RicardoMarquesCardoso/MicroLab/Microscope/Designs/[Top]Part1.DXF

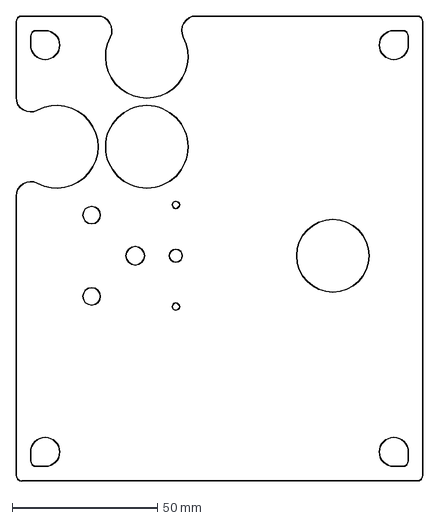
[picture p34: CAD file, 2020-10-22]
Microscope/Designs/[Top]Part1.DXF
140.0 x 160.0 mm
