RicardoMarquesCardoso/MicroLab/SyringePumps/Designs/Syringeholder2.DXF

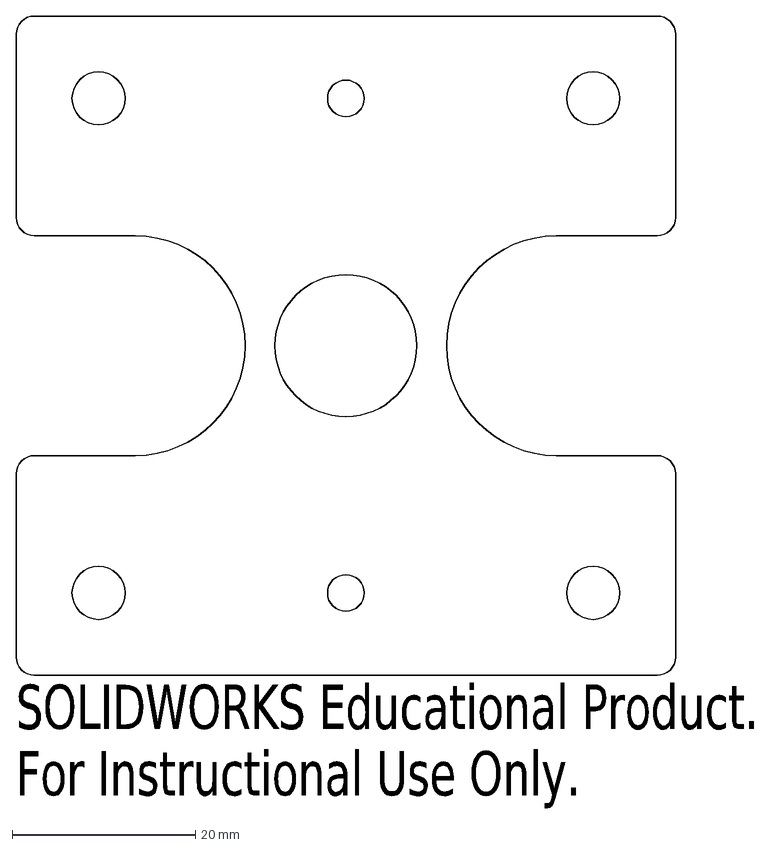
[picture p35: CAD file, 2020-11-19]
SyringePumps/Designs/Syringeholder2.DXF
SOLIDWORKS Educational Product.
For Instructional Use Only.
