RicardoMarquesCardoso/MicroLab/SyringePumps/Parts/Adapters/18mm.SLDPRT

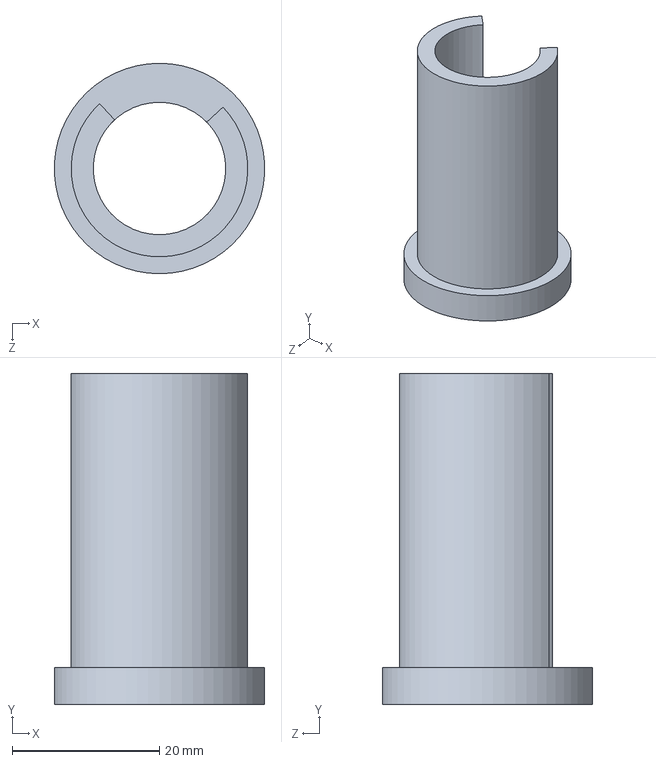
[picture p36: CAD file, 2020-11-19]
SyringePumps/Parts/Adapters/18mm.SLDPRT
28.6 x 45.0 x 28.6 mm
