RicardoMarquesCardoso/MicroLab/SyringePumps/Parts/MotorTop.SLDPRT

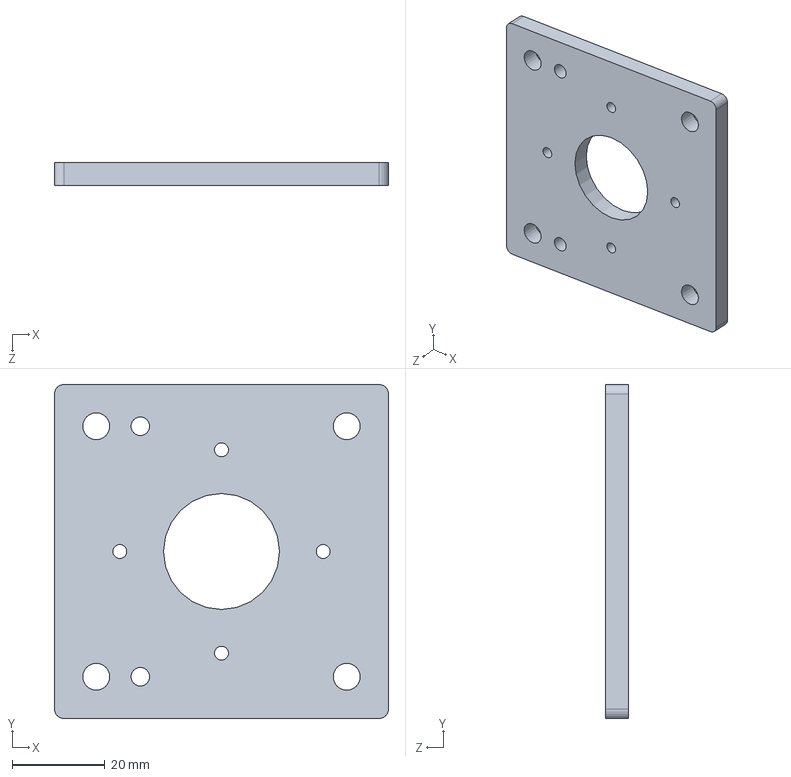
[picture p37: CAD file, 2020-11-19]
SyringePumps/Parts/MotorTop.SLDPRT
72.0 x 72.0 x 5.00 mm
