RicardoMarquesCardoso/MicroLab/Microscope/Designs/[MovingPiece]Top2.DXF

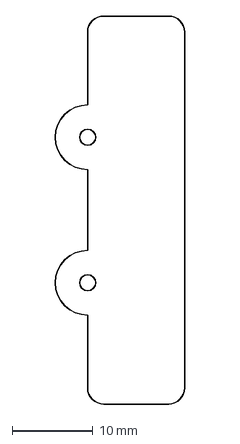
[picture p38: CAD file, 2020-10-22]
Microscope/Designs/[MovingPiece]Top2.DXF
16.0 x 48.0 mm
