RicardoMarquesCardoso/MicroLab/Microscope/Parts/Light.SLDPRT

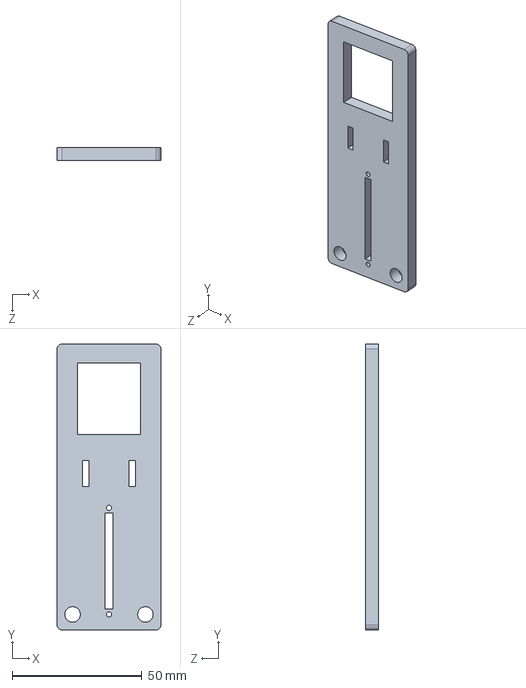
[picture p39: CAD file, 2020-10-22]
Microscope/Parts/Light.SLDPRT
40.0 x 110.0 x 5.00 mm
