RicardoMarquesCardoso/MicroLab/SyringePumps/Designs/MotorTop.DXF

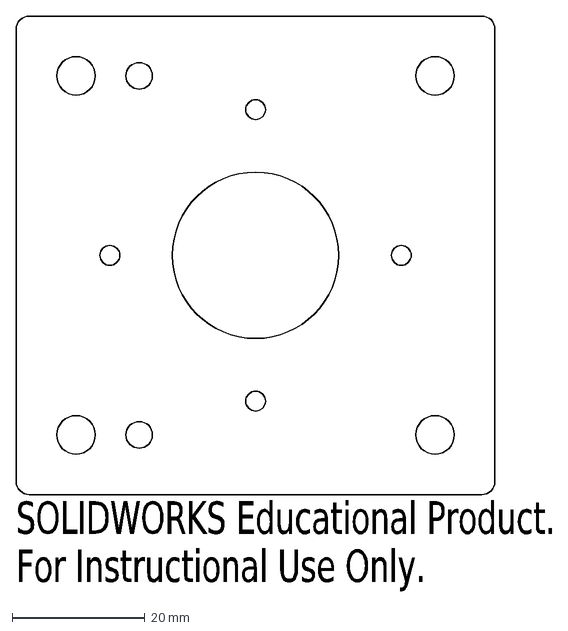
[picture p40: CAD file, 2020-11-19]
SyringePumps/Designs/MotorTop.DXF
SOLIDWORKS Educational Product.
For Instructional Use Only.
