RicardoMarquesCardoso/MicroLab/SyringePumps/Parts/movingpart2.SLDPRT

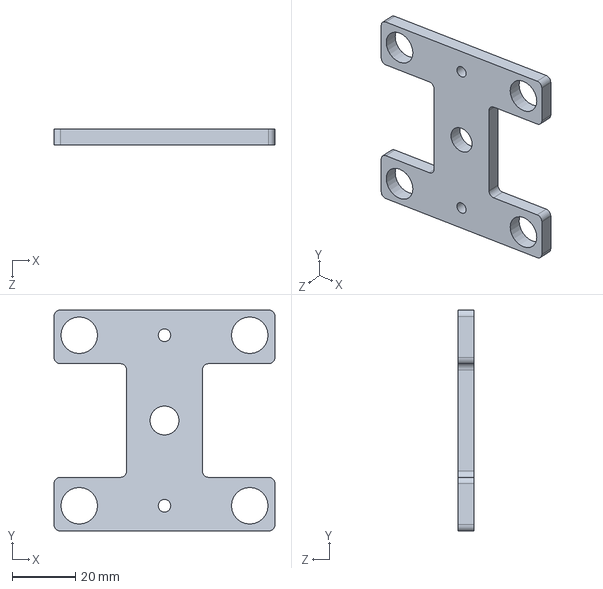
[picture p41: CAD file, 2020-11-19]
SyringePumps/Parts/movingpart2.SLDPRT
70.0 x 70.0 x 5.00 mm
