RicardoMarquesCardoso/MicroLab/Microscope/Designs/Light.DXF

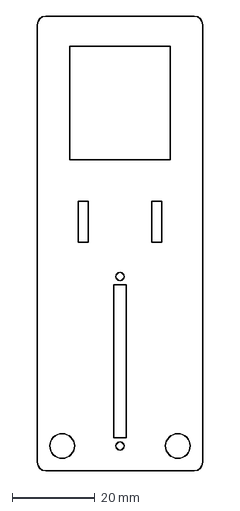
[picture p42: CAD file, 2020-10-22]
Microscope/Designs/Light.DXF
40.0 x 110.0 mm
