RicardoMarquesCardoso/MicroLab/Microscope/Parts/Bearing(LM6UU).SLDPRT

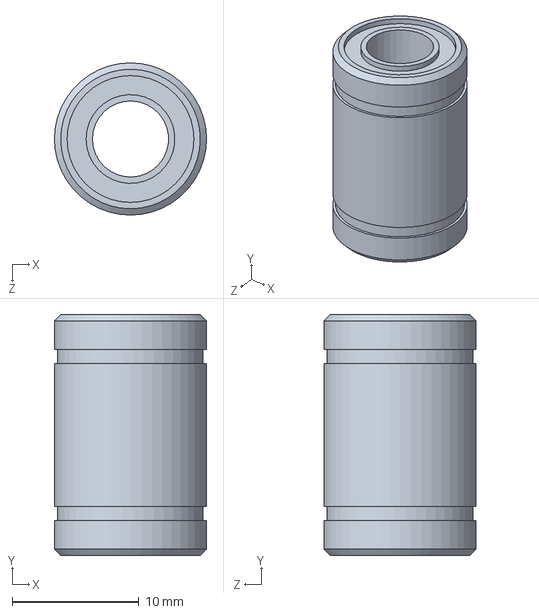
[picture p43: CAD file, 2020-10-22]
Microscope/Parts/Bearing(LM6UU).SLDPRT
12.0 x 19.0 x 12.0 mm
