RicardoMarquesCardoso/MicroLab/SyringePumps/Designs/movingpart.DXF

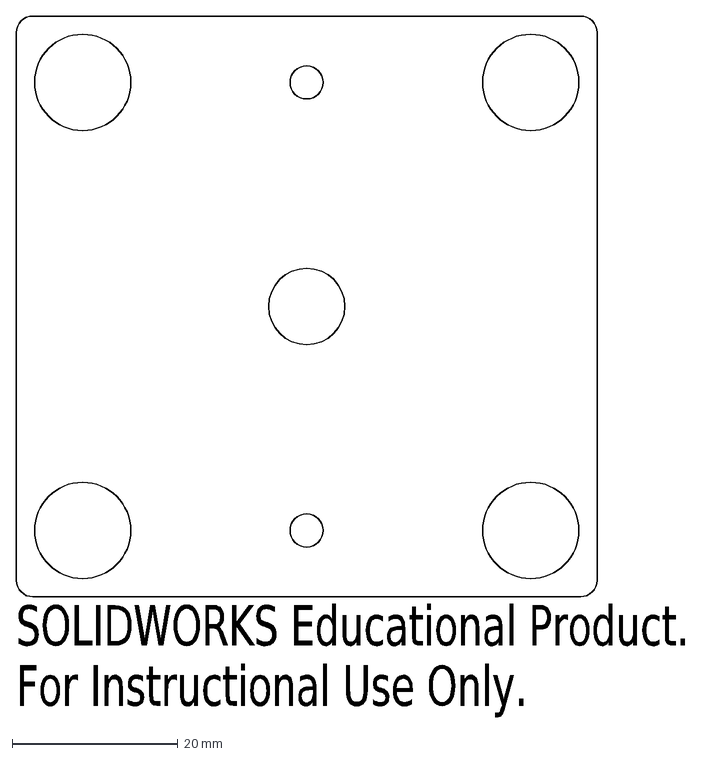
[picture p44: CAD file, 2020-11-19]
SyringePumps/Designs/movingpart.DXF
SOLIDWORKS Educational Product.
For Instructional Use Only.
