RicardoMarquesCardoso/MicroLab/SyringePumps/Parts/bar(35cm).SLDPRT

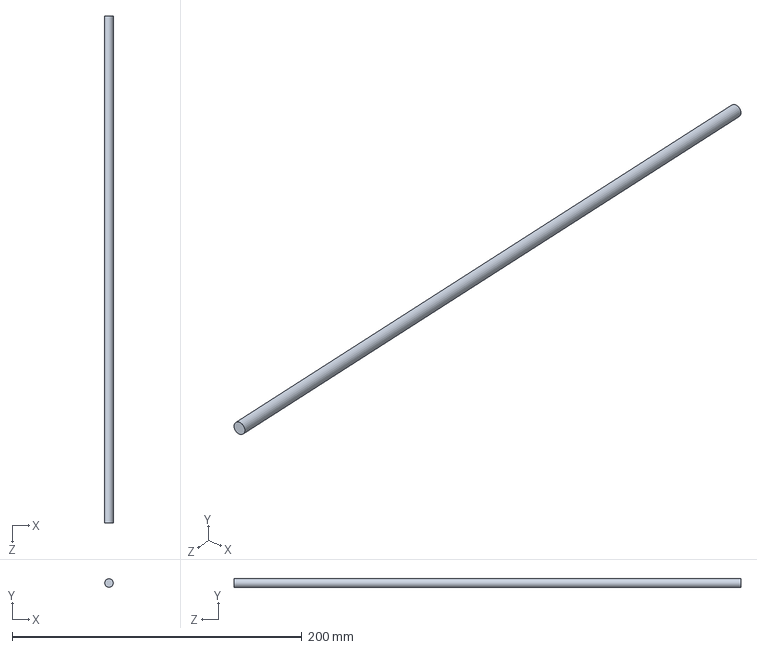
[picture p45: CAD file, 2020-11-19]
SyringePumps/Parts/bar(35cm).SLDPRT
6.00 x 6.00 x 350.0 mm
