RicardoMarquesCardoso/MicroLab/Microscope/Designs/[MovingPiece]Bottom.DXF

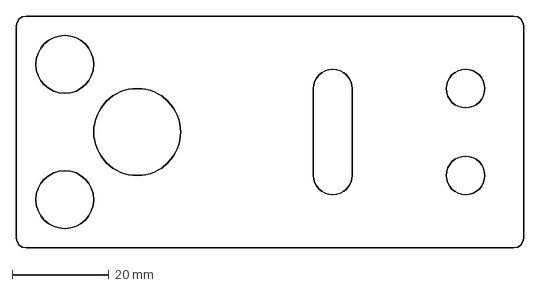
[picture p46: CAD file, 2020-10-22]
Microscope/Designs/[MovingPiece]Bottom.DXF
105.0 x 48.0 mm
