RicardoMarquesCardoso/MicroLab/Microscope/Parts/Bar7cm.SLDPRT

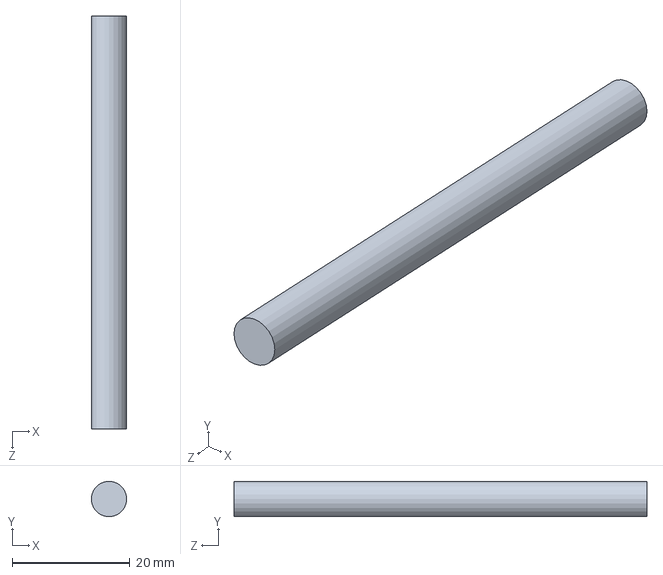
[picture p47: CAD file, 2020-10-22]
Microscope/Parts/Bar7cm.SLDPRT
6.00 x 6.00 x 70.0 mm
