RicardoMarquesCardoso/MicroLab/SyringePumps/Designs/Syringeholder1.DXF

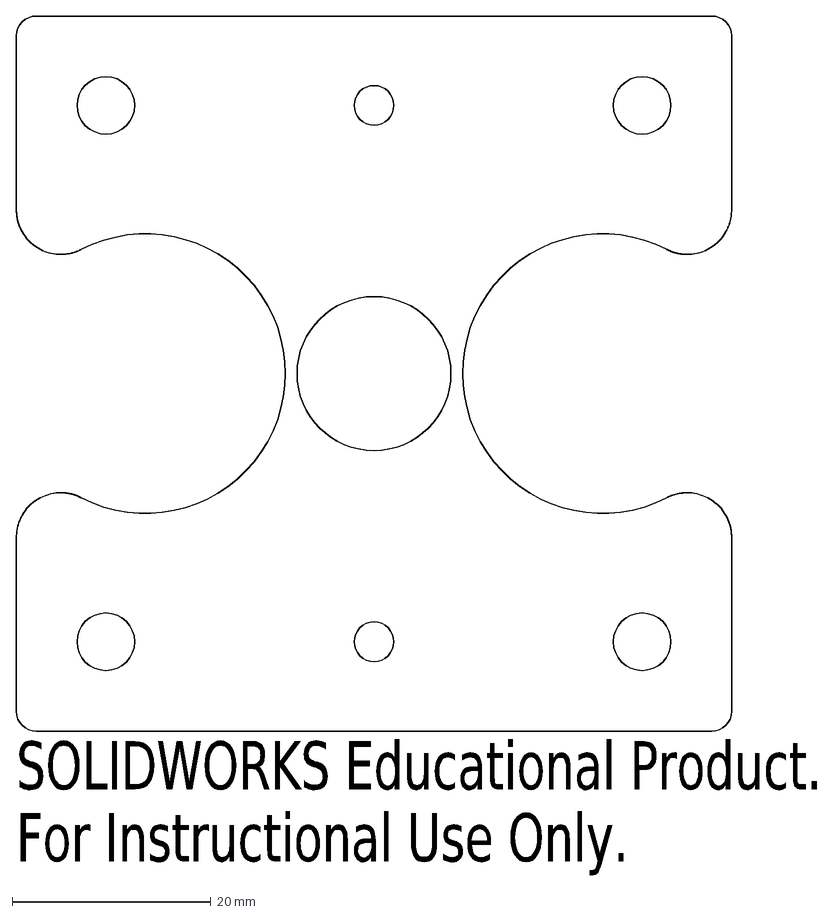
[picture p48: CAD file, 2020-11-19]
SyringePumps/Designs/Syringeholder1.DXF
SOLIDWORKS Educational Product.
For Instructional Use Only.
