RicardoMarquesCardoso/MicroLab/SyringePumps/Parts/Syringeholder1.SLDPRT

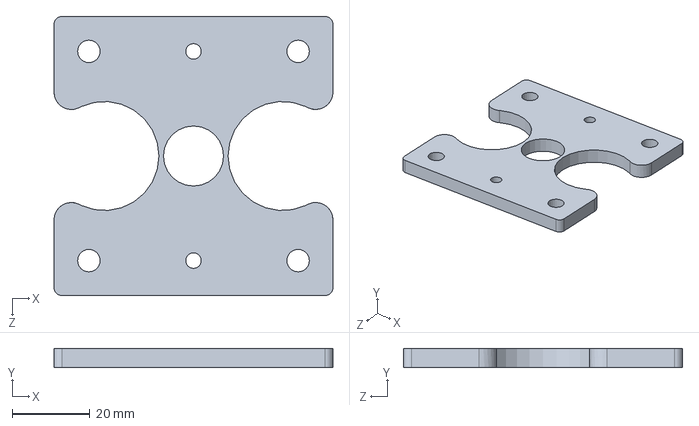
[picture p49: CAD file, 2020-11-19]
SyringePumps/Parts/Syringeholder1.SLDPRT
72.0 x 5.00 x 72.0 mm
