RicardoMarquesCardoso/MicroLab/Microscope/Parts/[MovingPiece]Bottom.SLDPRT

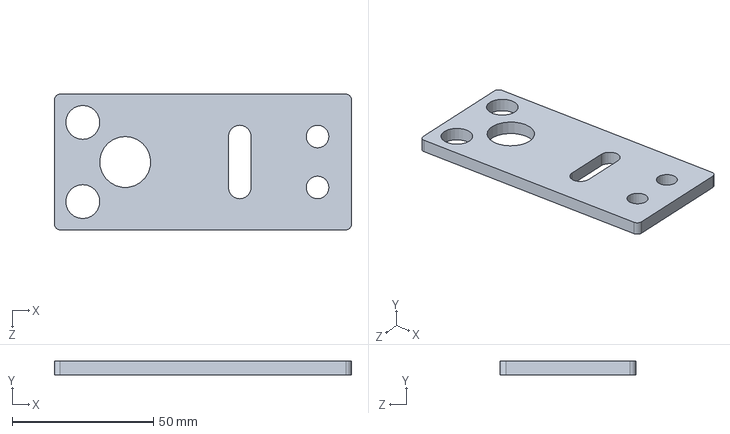
[picture p50: CAD file, 2020-10-22]
Microscope/Parts/[MovingPiece]Bottom.SLDPRT
105.0 x 5.00 x 48.0 mm
