RicardoMarquesCardoso/MicroLab/SyringePumps/Parts/syringeholder3.SLDPRT

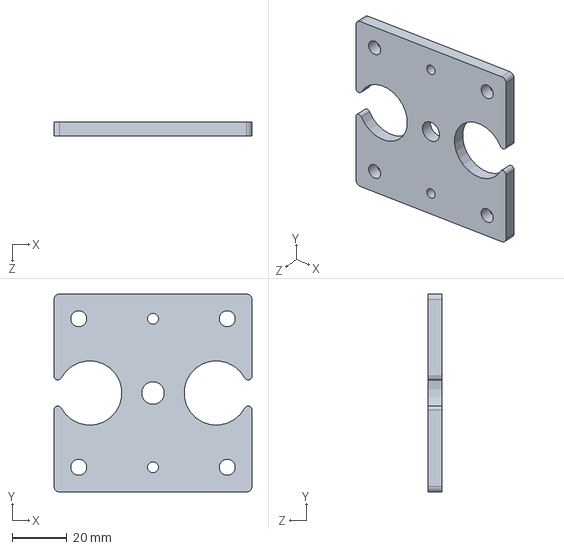
[picture p51: CAD file, 2020-11-19]
SyringePumps/Parts/syringeholder3.SLDPRT
72.0 x 72.0 x 5.00 mm
