RicardoMarquesCardoso/MicroLab/Microscope/Parts/[Top]Part2.SLDPRT

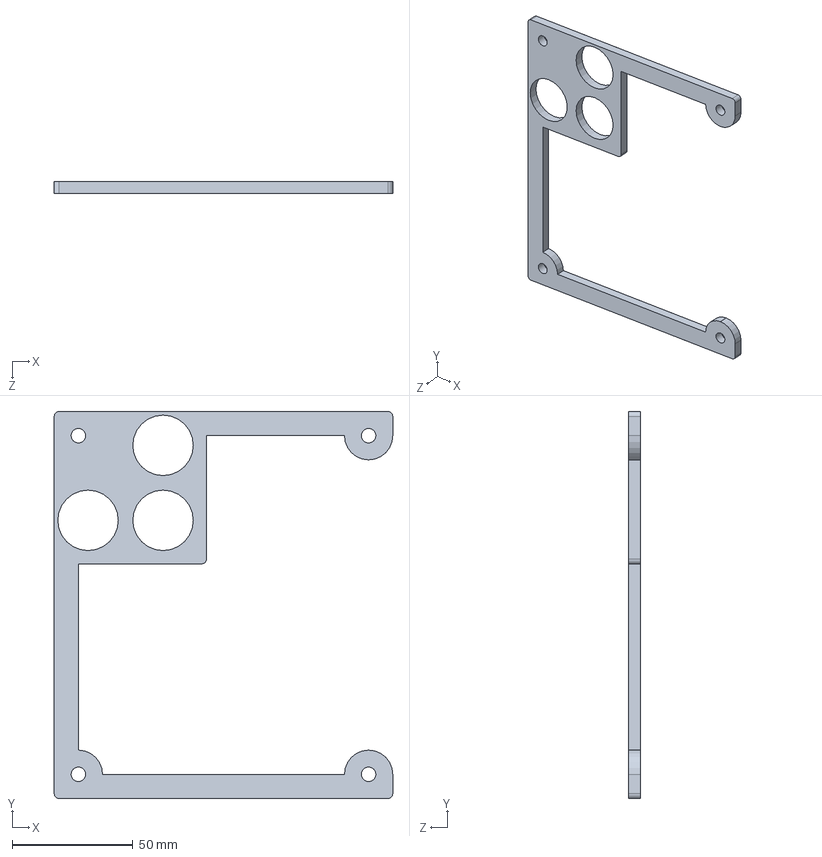
[picture p52: CAD file, 2020-10-22]
Microscope/Parts/[Top]Part2.SLDPRT
140.0 x 160.0 x 5.00 mm
