RicardoMarquesCardoso/MicroLab/Microscope/Parts/[MovingPiece]Top2.SLDPRT

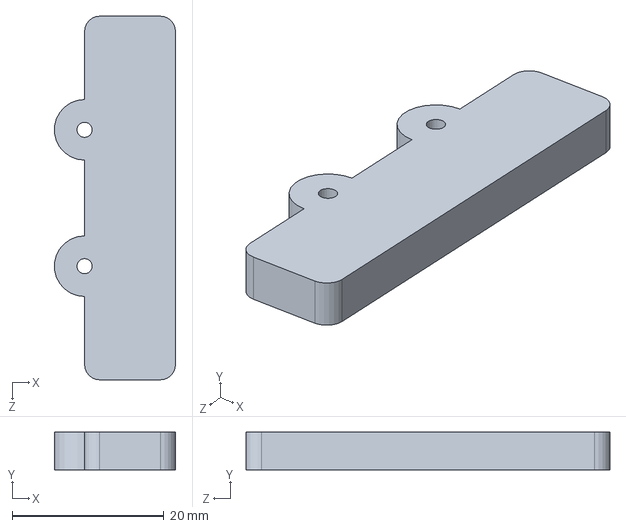
[picture p53: CAD file, 2020-10-22]
Microscope/Parts/[MovingPiece]Top2.SLDPRT
16.0 x 5.00 x 48.0 mm
