RicardoMarquesCardoso/MicroLab/SyringePumps/Parts/MotorBot2.SLDPRT

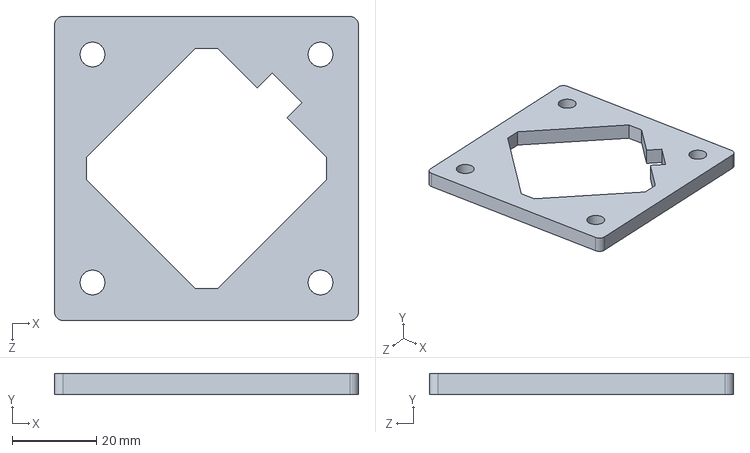
[picture p54: CAD file, 2020-11-19]
SyringePumps/Parts/MotorBot2.SLDPRT
72.0 x 5.00 x 72.0 mm
