RicardoMarquesCardoso/MicroLab/Microscope/Parts/[Top]Part1.SLDPRT

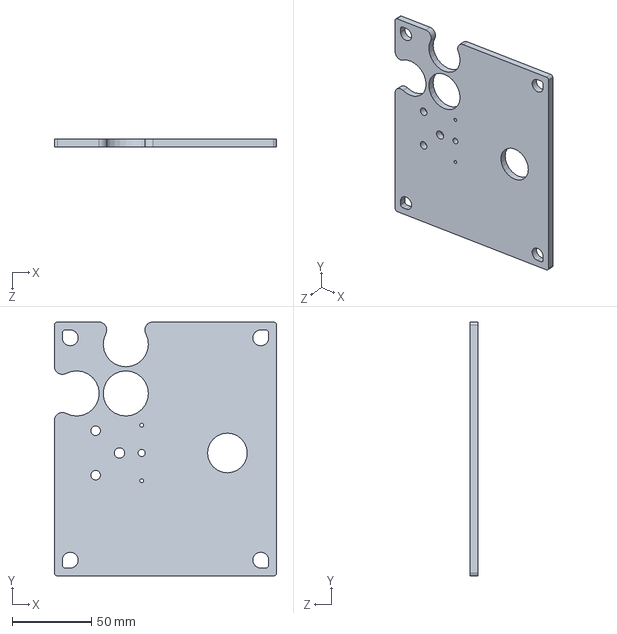
[picture p55: CAD file, 2020-10-22]
Microscope/Parts/[Top]Part1.SLDPRT
140.0 x 160.0 x 5.00 mm
