RicardoMarquesCardoso/MicroLab/Microscope/Parts/Nut(N80L5P).sldprt

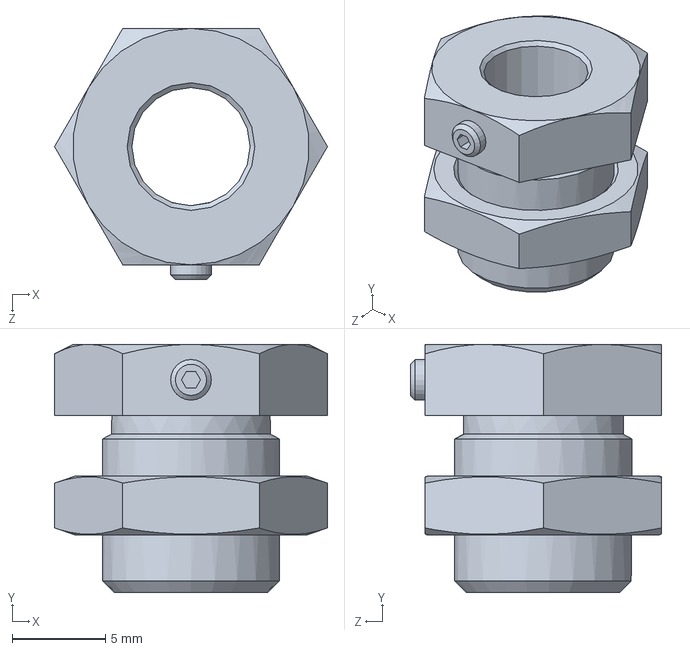
[picture p56: CAD file, 2020-10-22]
Microscope/Parts/Nut(N80L5P).sldprt
14.7 x 13.3 x 13.5 mm
