RicardoMarquesCardoso/MicroLab/Microscope/Parts/BottomPart.SLDPRT

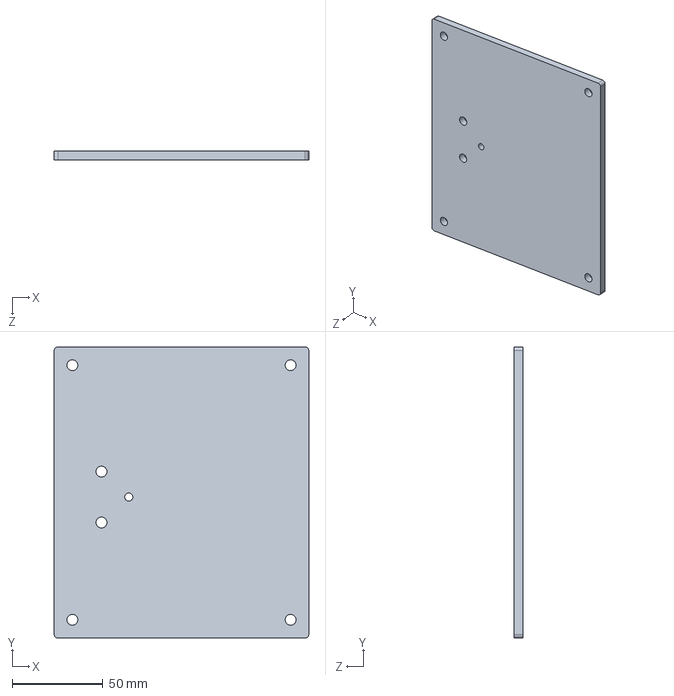
[picture p57: CAD file, 2020-10-22]
Microscope/Parts/BottomPart.SLDPRT
140.0 x 160.0 x 5.00 mm
