RicardoMarquesCardoso/MicroLab/Microscope/Parts/Collets.SLDPRT

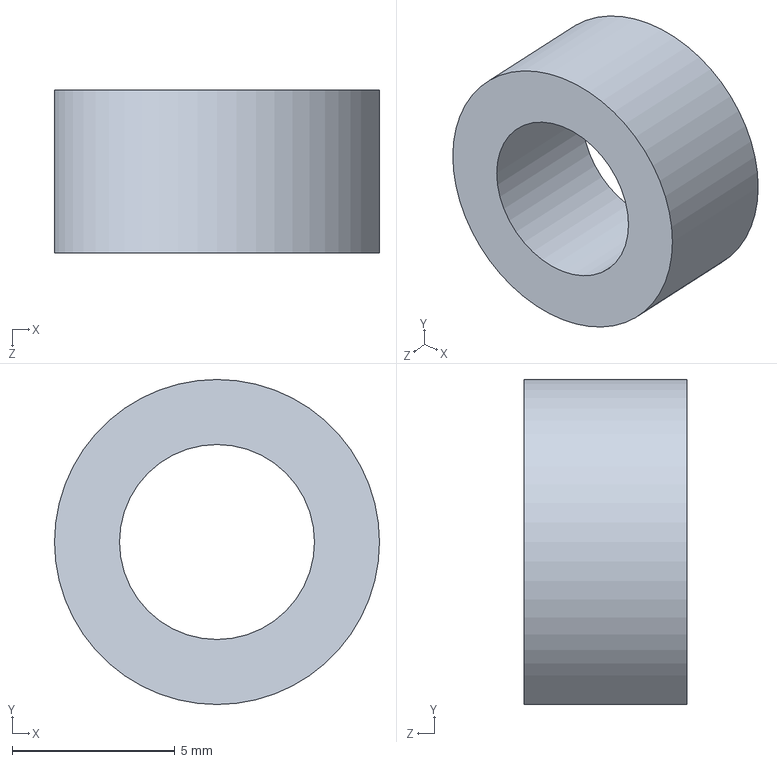
[picture p58: CAD file, 2020-10-22]
Microscope/Parts/Collets.SLDPRT
10.0 x 10.0 x 5.00 mm
