RicardoMarquesCardoso/MicroLab/Microscope/Parts/[PSeye]Part2.SLDPRT

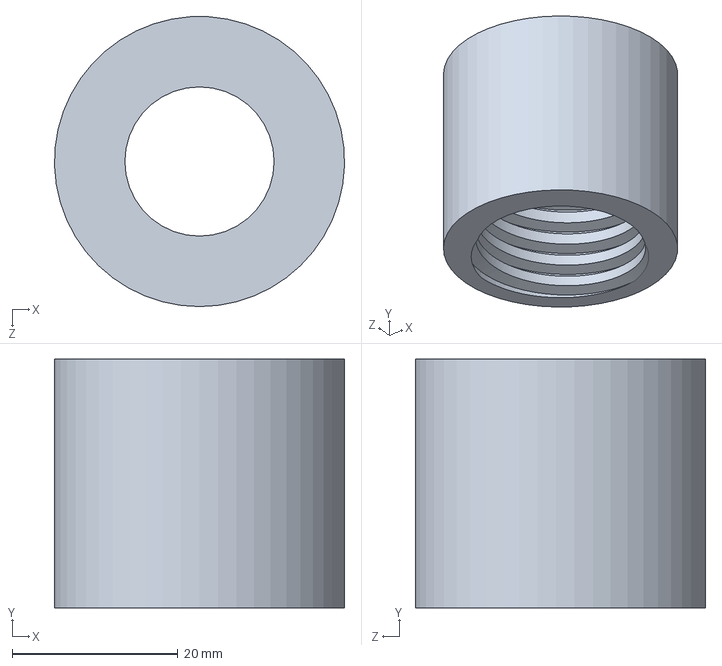
[picture p59: CAD file, 2020-10-01]
Microscope/Parts/[PSeye]Part2.SLDPRT
35.0 x 30.0 x 35.0 mm
