RicardoMarquesCardoso/MicroLab/Microscope/Parts/[PSeye]Part1.SLDPRT

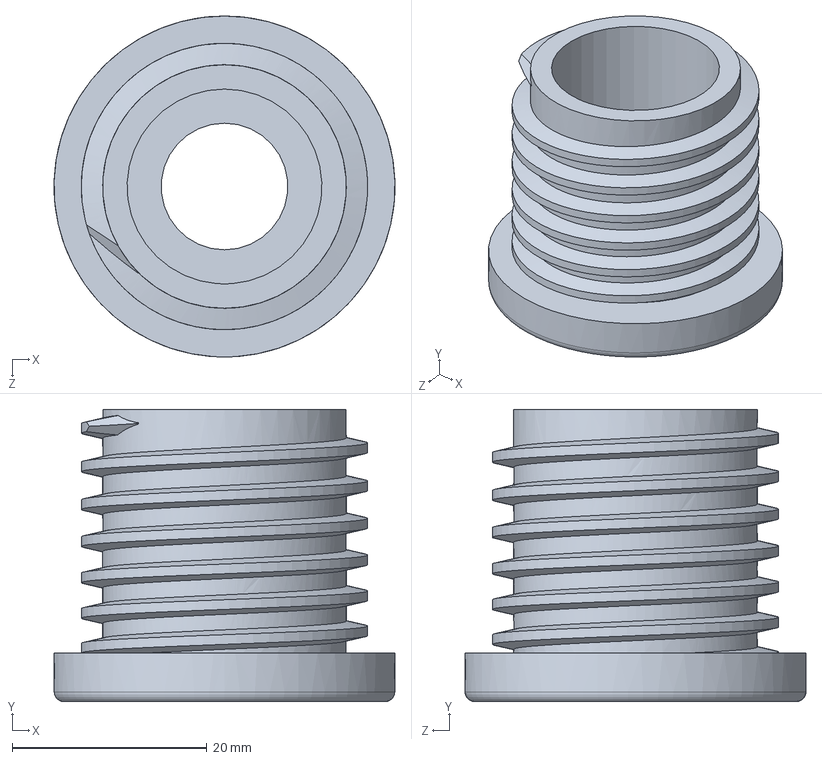
[picture p60: CAD file, 2020-10-01]
Microscope/Parts/[PSeye]Part1.SLDPRT
35.0 x 30.0 x 35.0 mm
